Rishvanth-SK-2002/8051-Digital-Clock/hardware/schematic/digclock.kicad_sch

## KiCad design hardware/schematic/digclock.kicad_sch (2026-09-27)

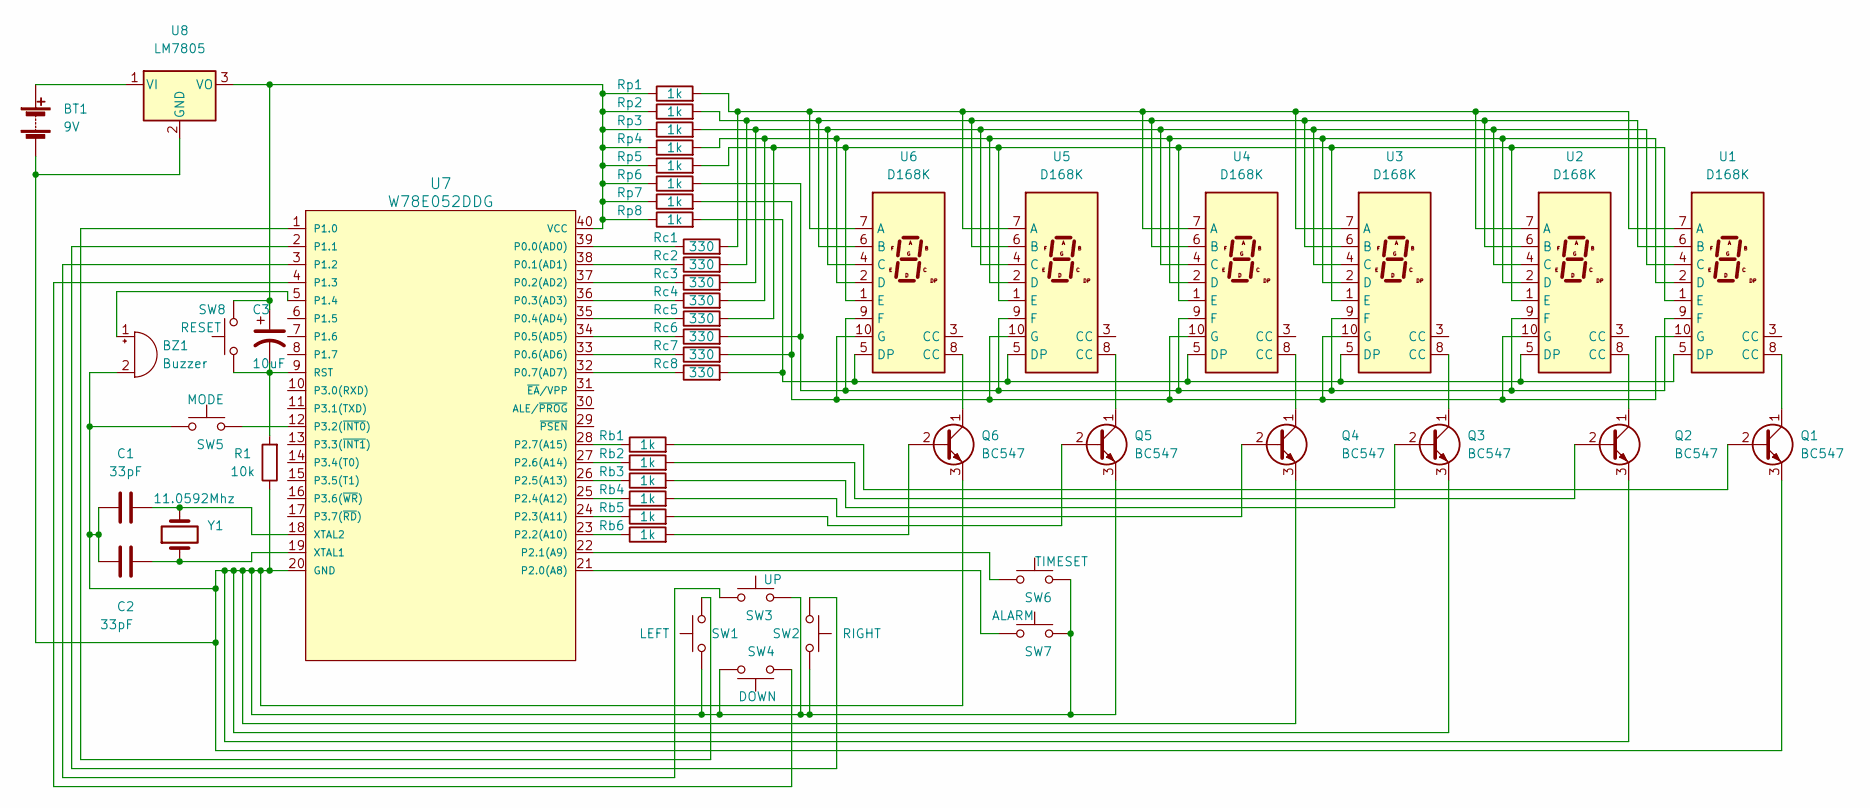
[picture p6: schematic digclock.kicad_sch]

Parts:
BT1: 9V; CP_Radial_D5.0mm_P2.00mm
BZ1: Buzzer; Buzzer_12x9.5RM7.6
C1, C2: 33pF; C_Radial_D5.0mm_H5.0mm_P2.00mm
C3: 10uF; CP_Radial_D5.0mm_P2.00mm
Q1, Q2, Q3, Q4, Q5, Q6: BC547; TO-92_Inline
R1: 10k; R_Axial_DIN0207_L6.3mm_D2.5mm_P7.62mm_Horizontal
Rb1, Rb2, Rb3, Rb4, Rb5, Rb6: 1k; R_Axial_DIN0207_L6.3mm_D2.5mm_P7.62mm_Horizontal
Rc1, Rc2, Rc3, Rc4, Rc5, Rc6, Rc7, Rc8: 330; R_Axial_DIN0207_L6.3mm_D2.5mm_P7.62mm_Horizontal
Rp1, Rp2, Rp3, Rp4, Rp5, Rp6, Rp7, Rp8: 1k; R_Axial_DIN0207_L6.3mm_D2.5mm_P7.62mm_Horizontal
SW1: LEFT; SW_PUSH_6mm
SW2: RIGHT; SW_PUSH_6mm
SW3: UP; SW_PUSH_6mm
SW4: DOWN; SW_PUSH_6mm
SW5: MODE; SW_PUSH_6mm
SW6: TIMESET; SW_PUSH_6mm
SW7: ALARM; SW_PUSH_6mm
SW8: RESET; SW_PUSH_6mm
U1, U2, U3, U4, U5, U6: D168K; D1X8K
U7: W78E052DDG; DIP-40_W15.24mm; MPN PIC16F877A-I/P; Digi-Key_PN PIC16F877A-I/P-ND
U8: LM7805; TO-220-3_Vertical
Y1: 11.0592Mhz; Crystal_HC49-U_Vertical

Connections:
unnamed: BT1.1 (+), U8.1 (VI)
unnamed: BT1.2 (-), BZ1.2 (+), C1.1, C2.1, Q1.3 (E), Q2.3 (E), Q3.3 (E), Q4.3 (E), Q5.3 (E), Q6.3 (E), R1.1, SW1.1, SW2.2, SW3.2, SW4.2, SW5.1, SW6.2, SW7.2, U7.20 (GND), U8.2 (GND)
unnamed: BZ1.1 (-), U7.5 (P1.4)
unnamed: C1.2, U7.18 (XTAL2), Y1.2
unnamed: C2.2, U7.19 (XTAL1), Y1.1
unnamed: C3.1, Rp1.1, Rp2.1, Rp3.1, Rp4.1, Rp5.1, Rp6.1, Rp7.1, Rp8.1, SW8.2, U7.40 (VCC), U8.3 (VO)
unnamed: C3.2, R1.2, SW8.1, U7.9 (RST)
unnamed: Q1.1 (C), U1.8 (CC)
unnamed: Q1.2 (B), Rb1.2
unnamed: Q2.1 (C), U2.8 (CC)
unnamed: Q2.2 (B), Rb2.2
unnamed: Q3.1 (C), U3.8 (CC)
unnamed: Q3.2 (B), Rb3.2
unnamed: Q4.1 (C), U4.8 (CC)
unnamed: Q4.2 (B), Rb4.2
unnamed: Q5.1 (C), U5.8 (CC)
unnamed: Q5.2 (B), Rb5.2
unnamed: Q6.1 (C), U6.8 (CC)
unnamed: Q6.2 (B), Rb6.2
unnamed: Rb1.1, U7.28 (P2.7(A15))
unnamed: Rb2.1, U7.27 (P2.6(A14))
unnamed: Rb3.1, U7.26 (P2.5(A13))
unnamed: Rb4.1, U7.25 (P2.4(A12))
unnamed: Rb5.1, U7.24 (P2.3(A11))
unnamed: Rb6.1, U7.23 (P2.2(A10))
unnamed: Rc1.1, U7.39 (P0.0(AD0))
unnamed: Rc1.2, Rp1.2, U1.7 (A), U2.7 (A), U3.7 (A), U4.7 (A), U5.7 (A), U6.7 (A)
unnamed: Rc2.1, U7.38 (P0.1(AD1))
unnamed: Rc2.2, Rp2.2, U1.6 (B), U2.6 (B), U3.6 (B), U4.6 (B), U5.6 (B), U6.6 (B)
unnamed: Rc3.1, U7.37 (P0.2(AD2))
unnamed: Rc3.2, Rp3.2, U1.4 (C), U2.4 (C), U3.4 (C), U4.4 (C), U5.4 (C), U6.4 (C)
unnamed: Rc4.1, U7.36 (P0.3(AD3))
unnamed: Rc4.2, Rp4.2, U1.2 (D), U2.2 (D), U3.2 (D), U4.2 (D), U5.2 (D), U6.2 (D)
unnamed: Rc5.1, U7.35 (P0.4(AD4))
unnamed: Rc5.2, Rp5.2, U1.1 (E), U2.1 (E), U3.1 (E), U4.1 (E), U5.1 (E), U6.1 (E)
unnamed: Rc6.1, U7.34 (P0.5(AD5))
unnamed: Rc6.2, Rp6.2, U1.9 (F), U2.9 (F), U3.9 (F), U4.9 (F), U5.9 (F), U6.9 (F)
unnamed: Rc7.1, U7.33 (P0.6(AD6))
unnamed: Rc7.2, Rp7.2, U1.10 (G), U2.10 (G), U3.10 (G), U4.10 (G), U5.10 (G), U6.10 (G)
unnamed: Rc8.1, U7.32 (P0.7(AD7))
unnamed: Rc8.2, Rp8.2, U1.5 (DP), U2.5 (DP), U3.5 (DP), U4.5 (DP), U5.5 (DP), U6.5 (DP)
unnamed: SW1.2, U7.1 (P1.0)
unnamed: SW2.1, U7.2 (P1.1)
unnamed: SW3.1, U7.3 (P1.2)
unnamed: SW4.1, U7.4 (P1.3)
unnamed: SW5.2, U7.12 (P3.2(~INT0))
unnamed: SW6.1, U7.22 (P2.1(A9))
unnamed: SW7.1, U7.21 (P2.0(A8))
